eosti/metamer-sao/kicad/OUTPUTS/DOCS/MetamerBoard-0.png

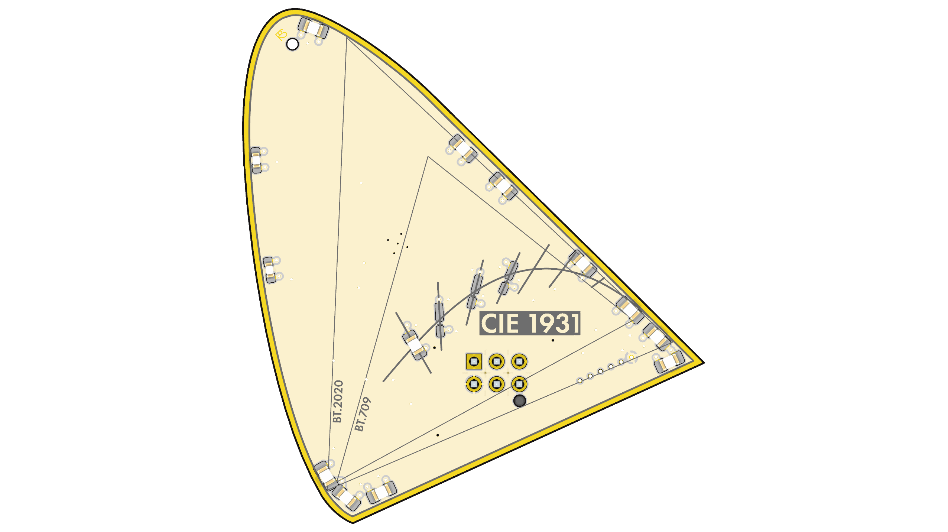
kicad/OUTPUTS/DOCS/MetamerBoard-0.png
