eosti/metamer-sao/python_graphs/apple.png

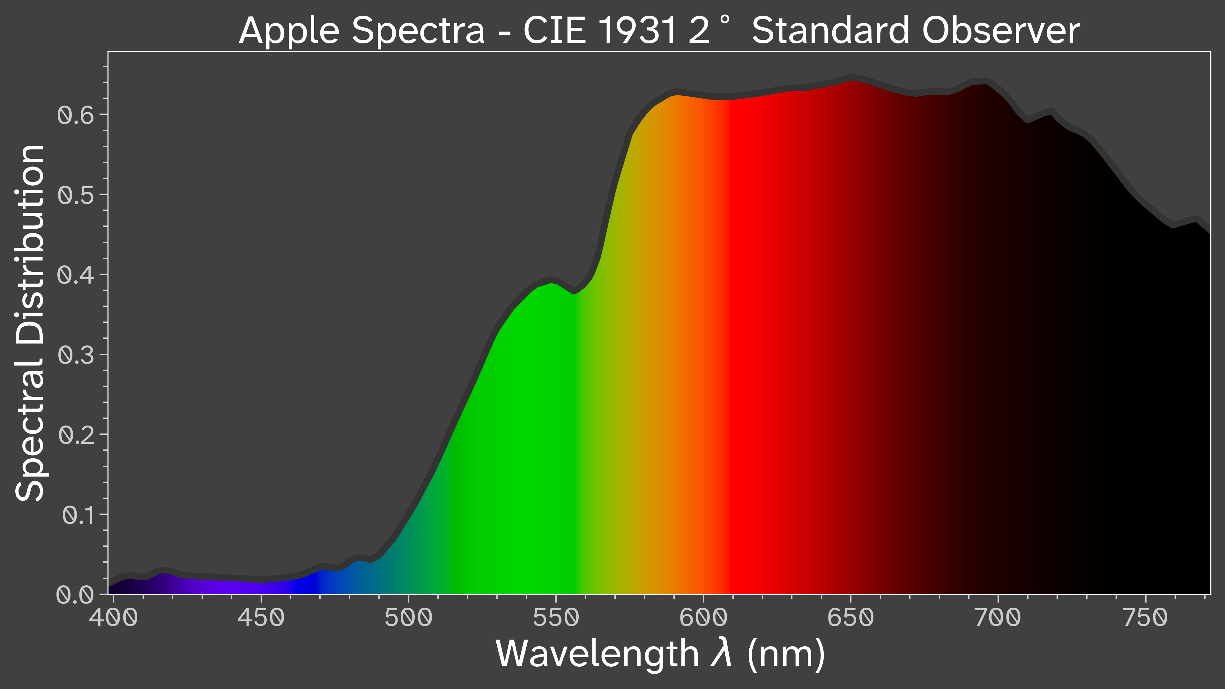
python_graphs/apple.png
