eosti/metamer-sao/python_graphs/appleInLED.png

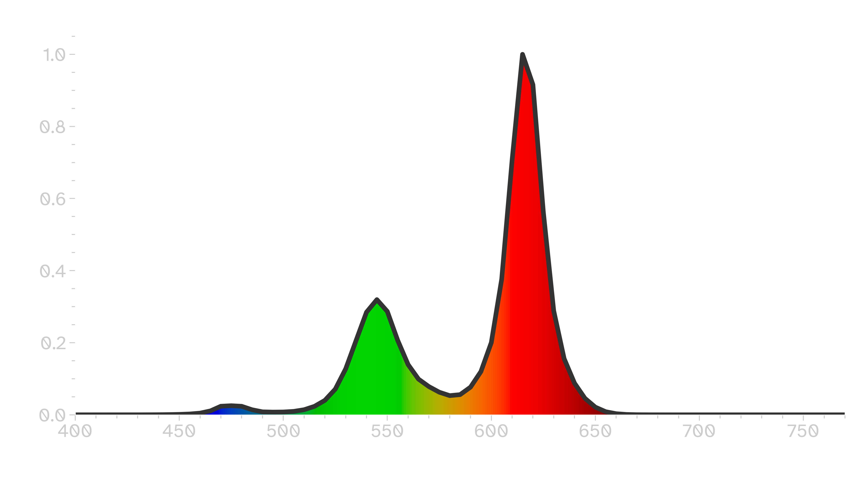
python_graphs/appleInLED.png
