eosti/metamer-sao/python_graphs/appleInSun.png

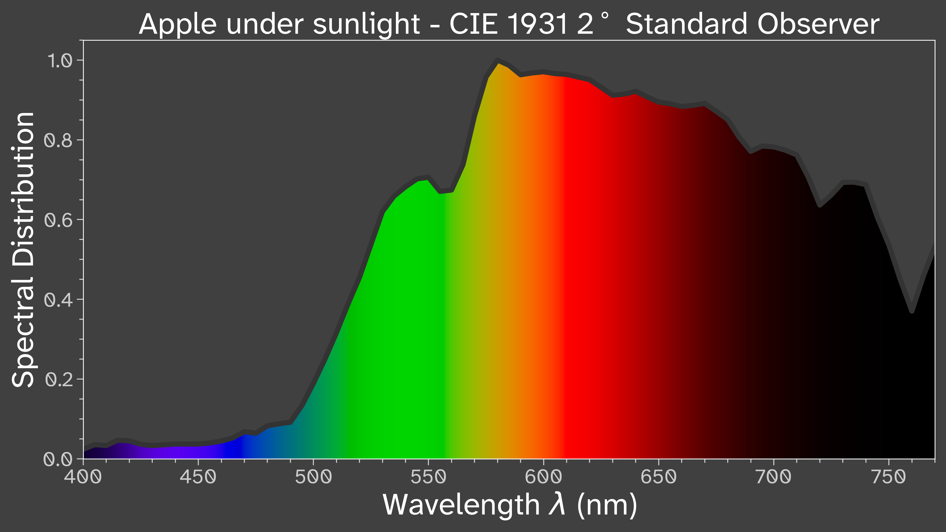
python_graphs/appleInSun.png
