eosti/metamer-sao/python_graphs/blackbody_illuminant.png

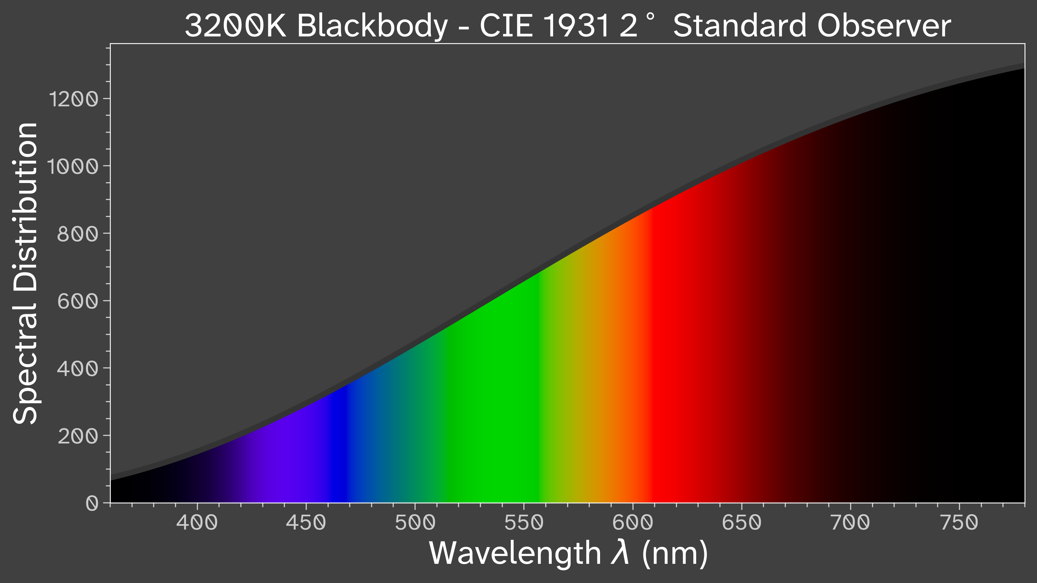
python_graphs/blackbody_illuminant.png
