eosti/metamer-sao/python_graphs/cie1931_cmf.png

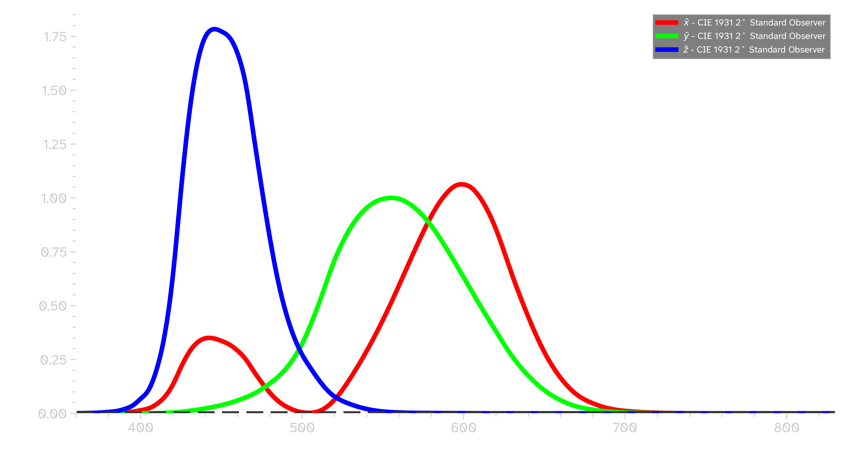
python_graphs/cie1931_cmf.png
