eosti/metamer-sao/python_graphs/cie1931_gamut.png

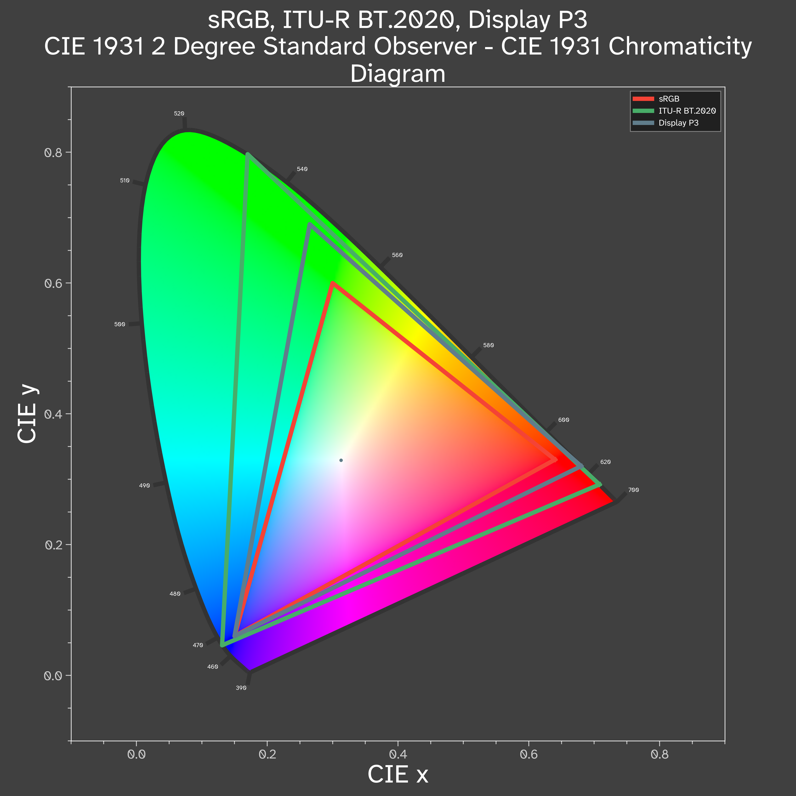
python_graphs/cie1931_gamut.png
