eosti/metamer-sao/python_graphs/cie1931_rgb_points.png

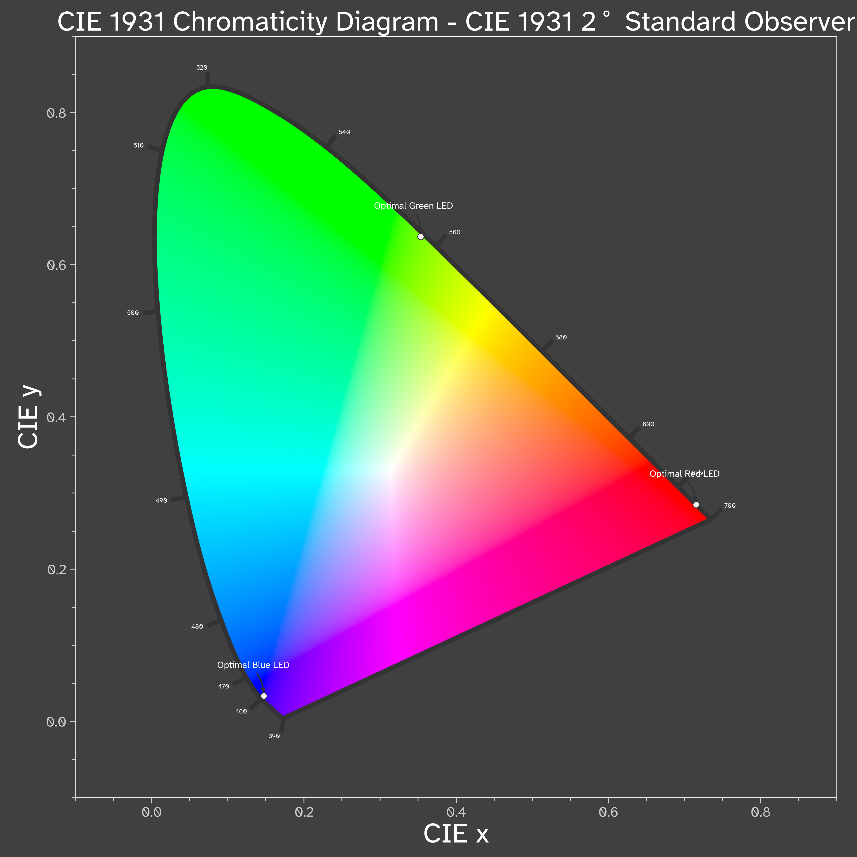
python_graphs/cie1931_rgb_points.png
