eosti/metamer-sao/python_graphs/D65_illuminant.png

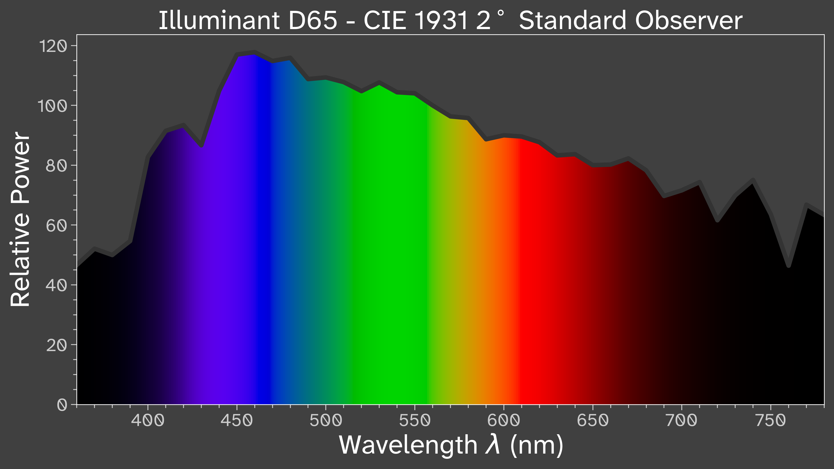
python_graphs/D65_illuminant.png
