eosti/metamer-sao/python_graphs/ideal_cmfs.png

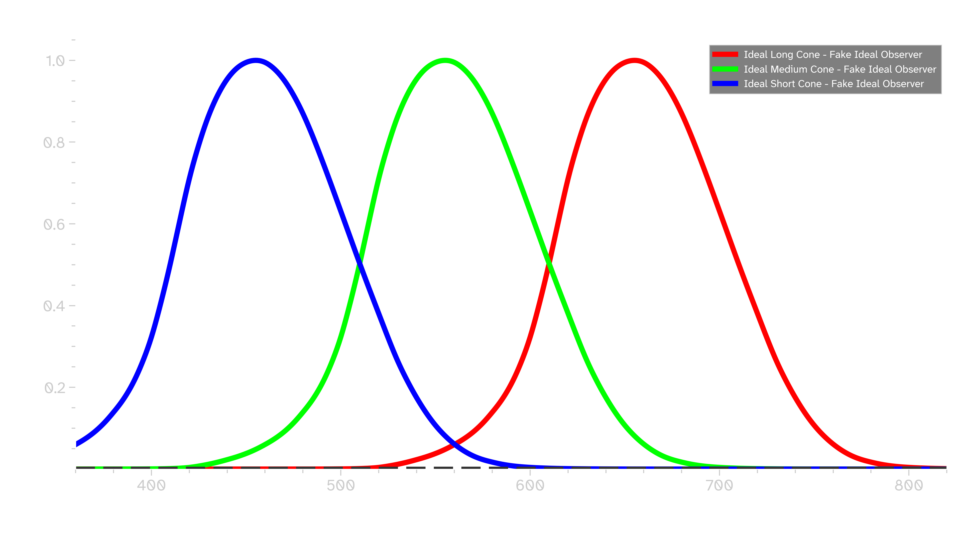
python_graphs/ideal_cmfs.png
