eosti/metamer-sao/python_graphs/ideal_leds_superimpose.png

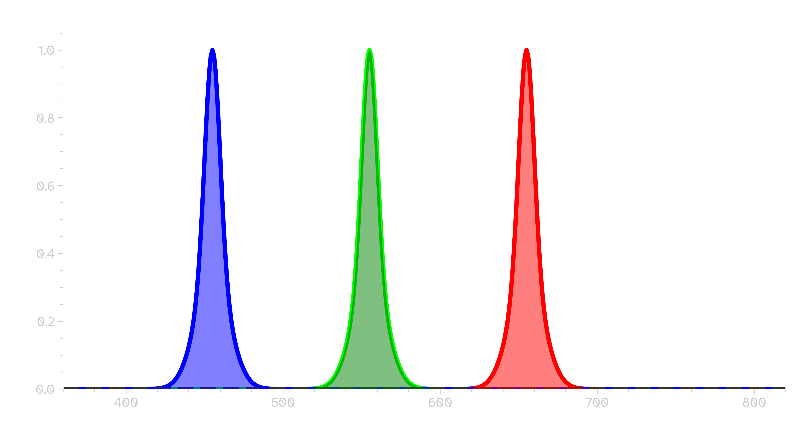
python_graphs/ideal_leds_superimpose.png
