eosti/metamer-sao/python_graphs/medium_apple.png

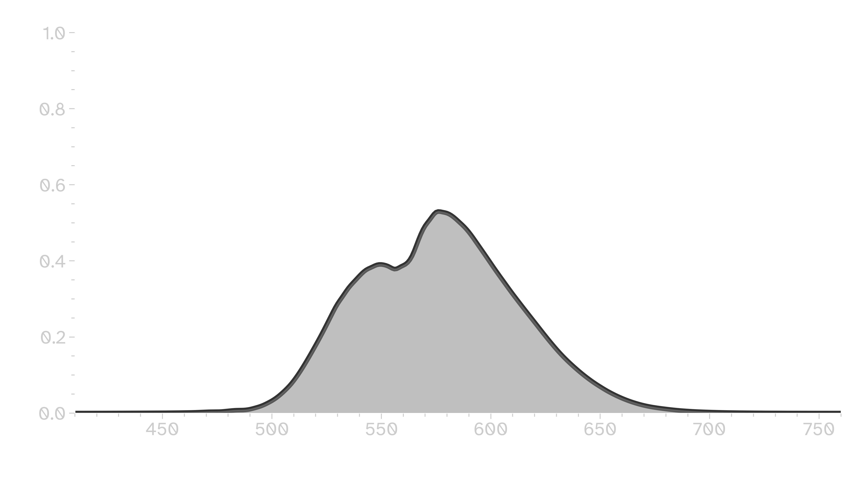
python_graphs/medium_apple.png
