eosti/metamer-sao/python_graphs/medium_cmf.png

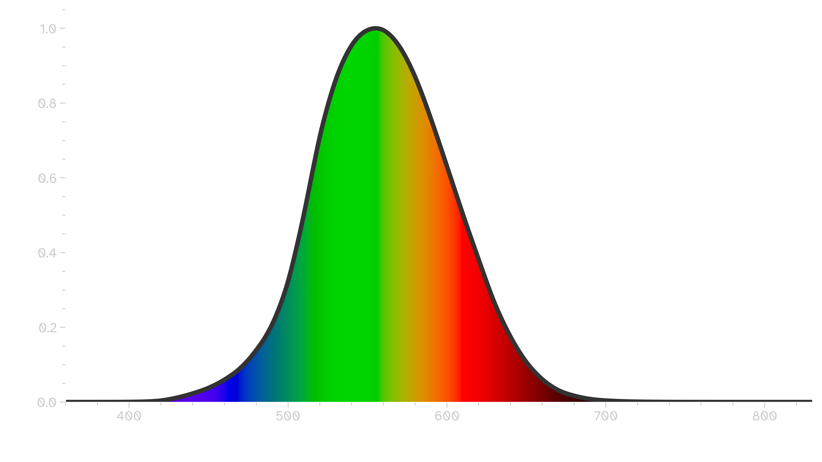
python_graphs/medium_cmf.png
