eosti/metamer-sao/python_graphs/real_leds_superimpose.png

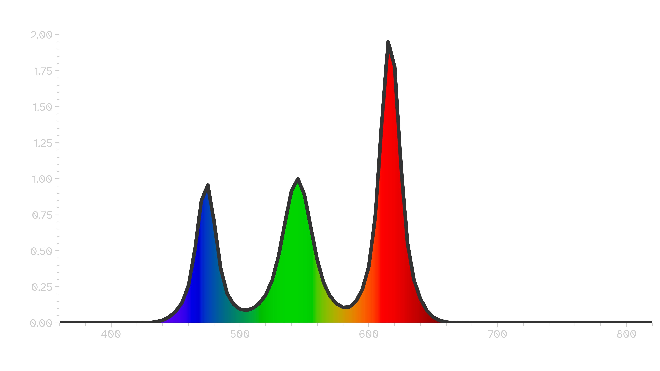
python_graphs/real_leds_superimpose.png
