eosti/metamer-sao/python_graphs/sao_illuminant.png

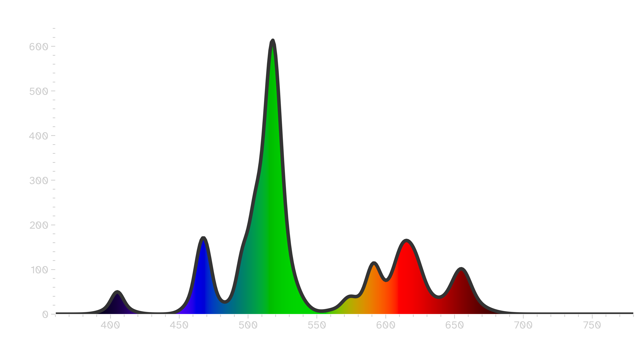
python_graphs/sao_illuminant.png
