eosti/metamer-sao/python_graphs/teal_illuminant.png

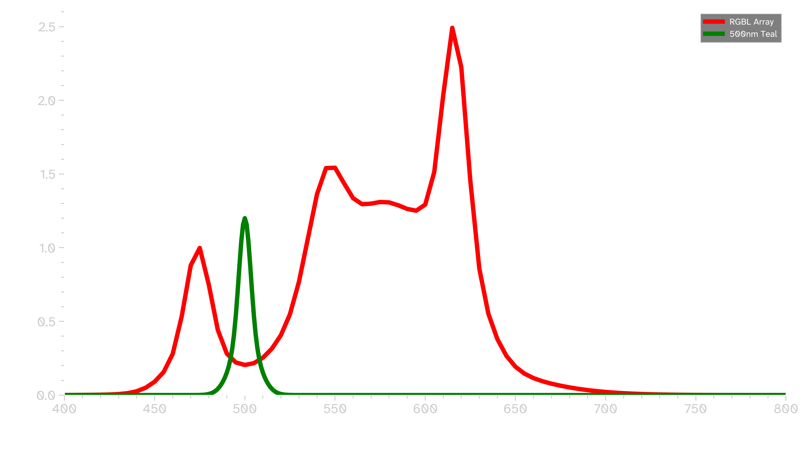
python_graphs/teal_illuminant.png
