eosti/metamer-sao/python_graphs/white_illuminant.png

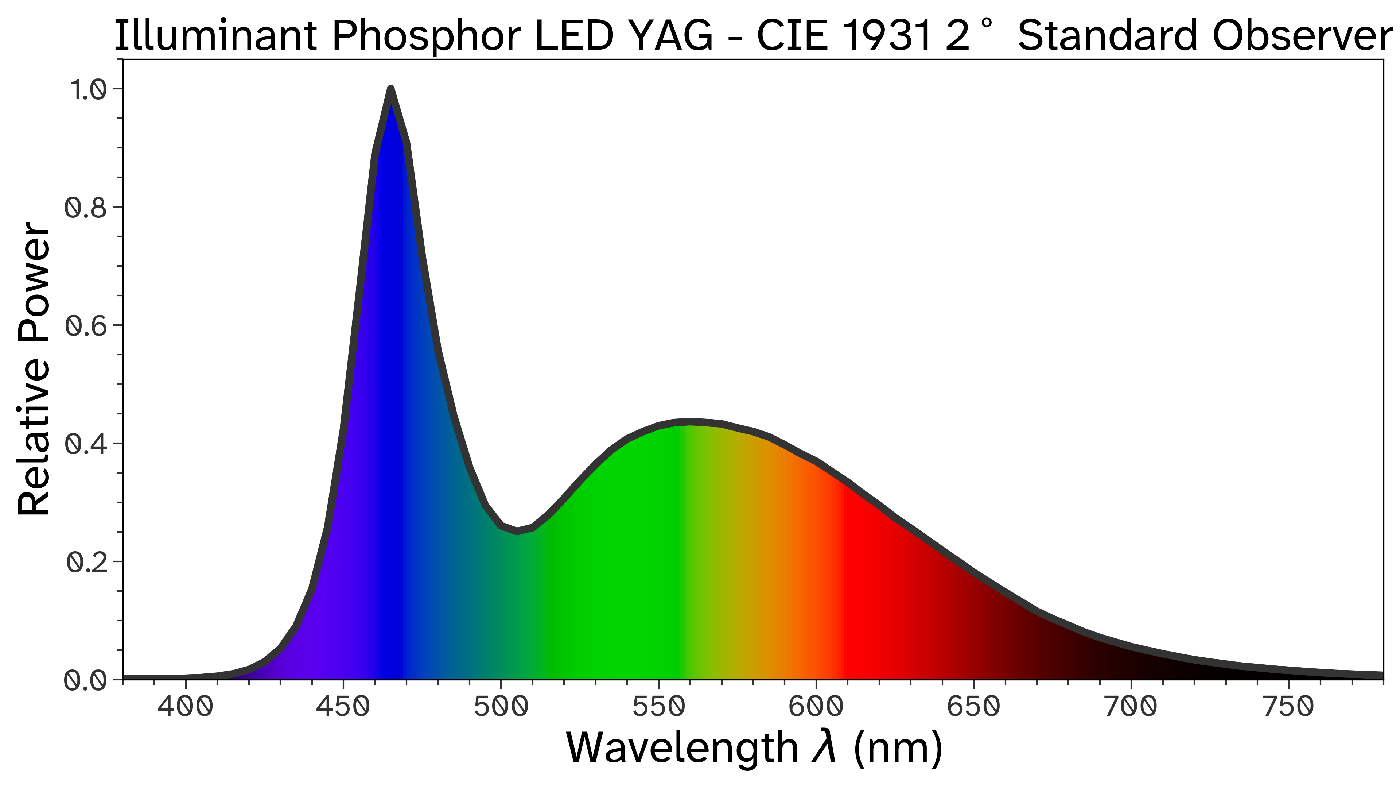
python_graphs/white_illuminant.png
