eosti/metamer-sao/python_graphs/build_amber.png

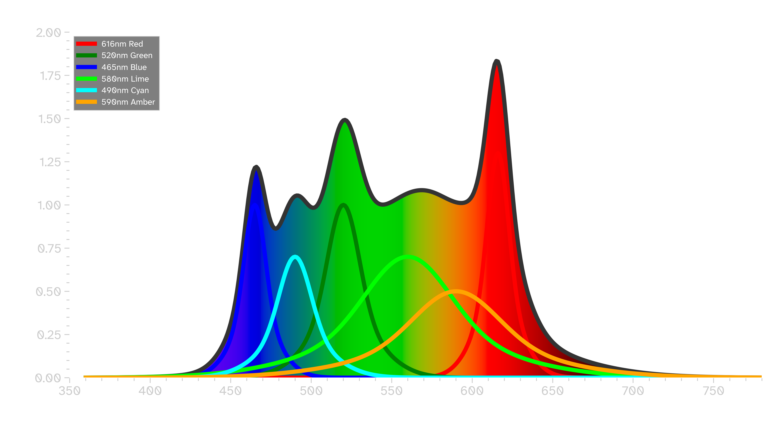
python_graphs/build_amber.png
