eosti/metamer-sao/python_graphs/build_cyan.png

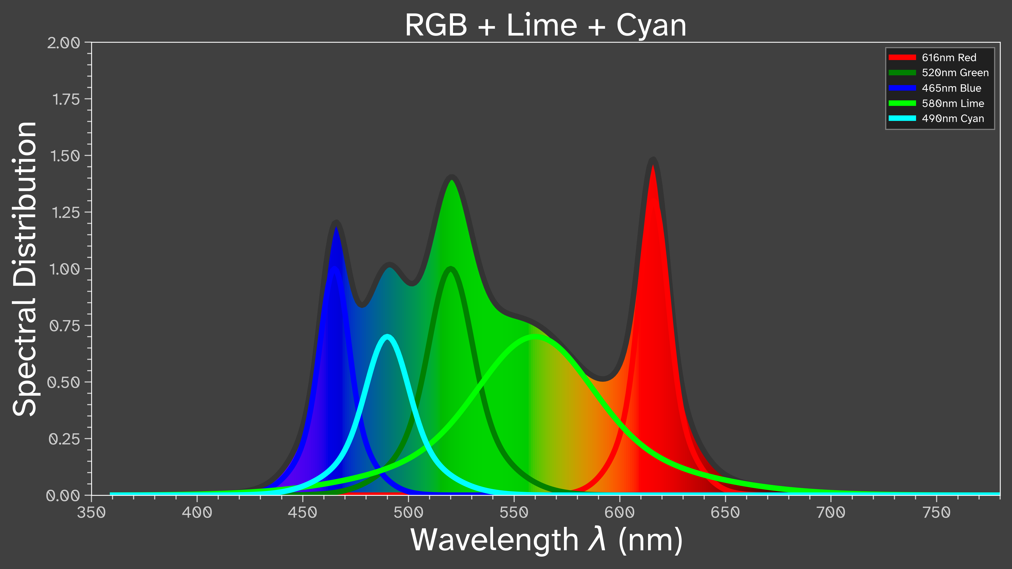
python_graphs/build_cyan.png
