eosti/metamer-sao/python_graphs/build_lime.png

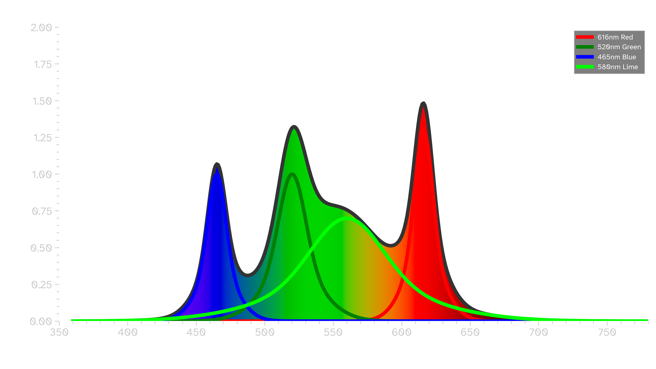
python_graphs/build_lime.png
