eosti/metamer-sao/python_graphs/build_rgb.png

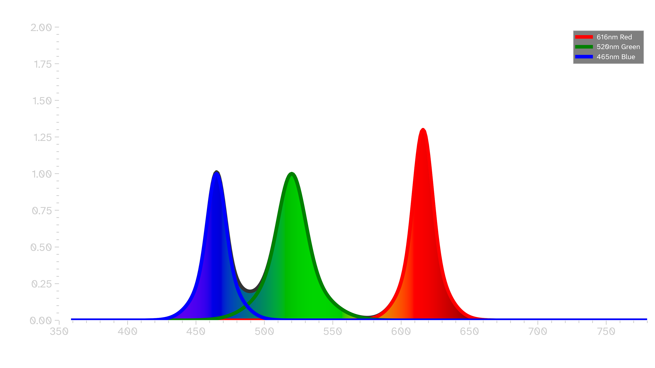
python_graphs/build_rgb.png
